todbot/blinkm2/schematic/blinkm_mk2c.brd

## EAGLE design schematic/blinkm_mk2c.brd (2014-01-24)

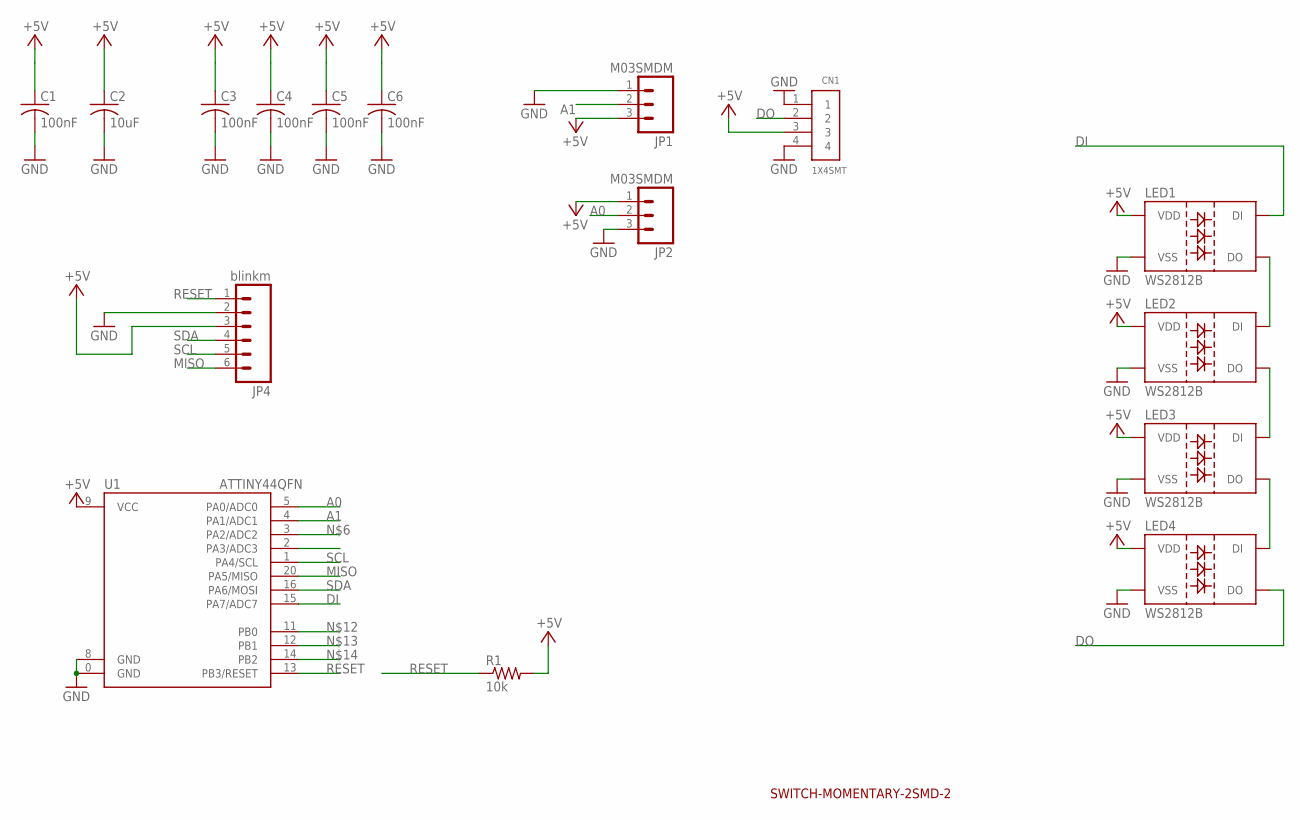
[picture p14: schematic blinkm_mk2c.sch]

Parts:
C1, C3, C4, C5, C6: 100nF; C0603
C2: 10uF; C0603
CN1: 1X4SMT; 1X4-SMT
JP1, JP2: M03SMDM; 1X03-SMD-MINIMAL
JP4: blinkm; 1X06_LOCK
LED1, LED2, LED3, LED4: WS2812B
R1: 10k; R0603
U1: ATTINY44QFN; QFN20

Connections:
+5V: C1.1, C2.1, C3.1, C4.1, C5.1, C6.1, CN1.3, JP1.3, JP2.1, JP4.3, LED1.1 (VDD), LED2.1 (VDD), LED3.1 (VDD), LED4.1 (VDD), R1.2, U1.9 (VCC)
A0: JP2.2, U1.5 (PA0/ADC0)
A1: JP1.2, U1.4 (PA1/ADC1)
DI: LED1.4 (DI), U1.15 (PA7/ADC7); also elsewhere on the board
DO: CN1.2, LED4.2 (DO)
GND: C1.2, C2.2, C3.2, C4.2, C5.2, C6.2, CN1.1, CN1.4, JP1.1, JP2.3, JP4.2, LED1.3 (VSS), LED2.3 (VSS), LED3.3 (VSS), LED4.3 (VSS), U1.0 (GND), U1.8 (GND); also elsewhere on the board
MISO: JP4.6, U1.20 (PA5/MISO)
unnamed: LED1.2 (DO), LED2.4 (DI)
unnamed: LED2.2 (DO), LED3.4 (DI)
unnamed: LED3.2 (DO), LED4.4 (DI)
RESET: JP4.1, R1.1, U1.13 (PB3/RESET)
SCL: JP4.5, U1.1 (PA4/SCL)
SDA: JP4.4, U1.16 (PA6/MOSI)

Notes on the sheet:
SWITCH-MOMENTARY-2SMD-2

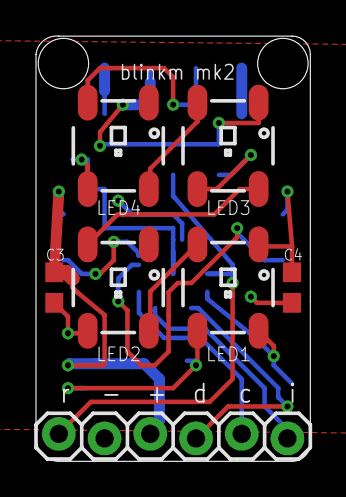
[picture p15: board blinkm_mk2c.brd from above]

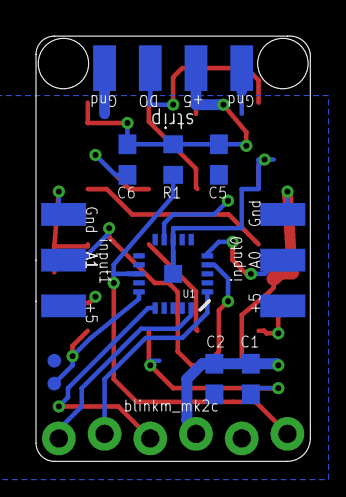
[picture p16: board blinkm_mk2c.brd from below]

Board: 2 copper layers, 15.2 x 23.6 mm, 18 parts (11 on the bottom side), 13 nets.

Other parts of the board:
TP1, TP2: TEST-POINT3; PAD.03X.03

Their connections:
DI: TP1.P$1; also elsewhere on the board
GND: TP2.P$1; also elsewhere on the board
