todbot/blinkm2/schematic/blinkm_mk2b.brd

## EAGLE design schematic/blinkm_mk2b.brd (2013-06-05)

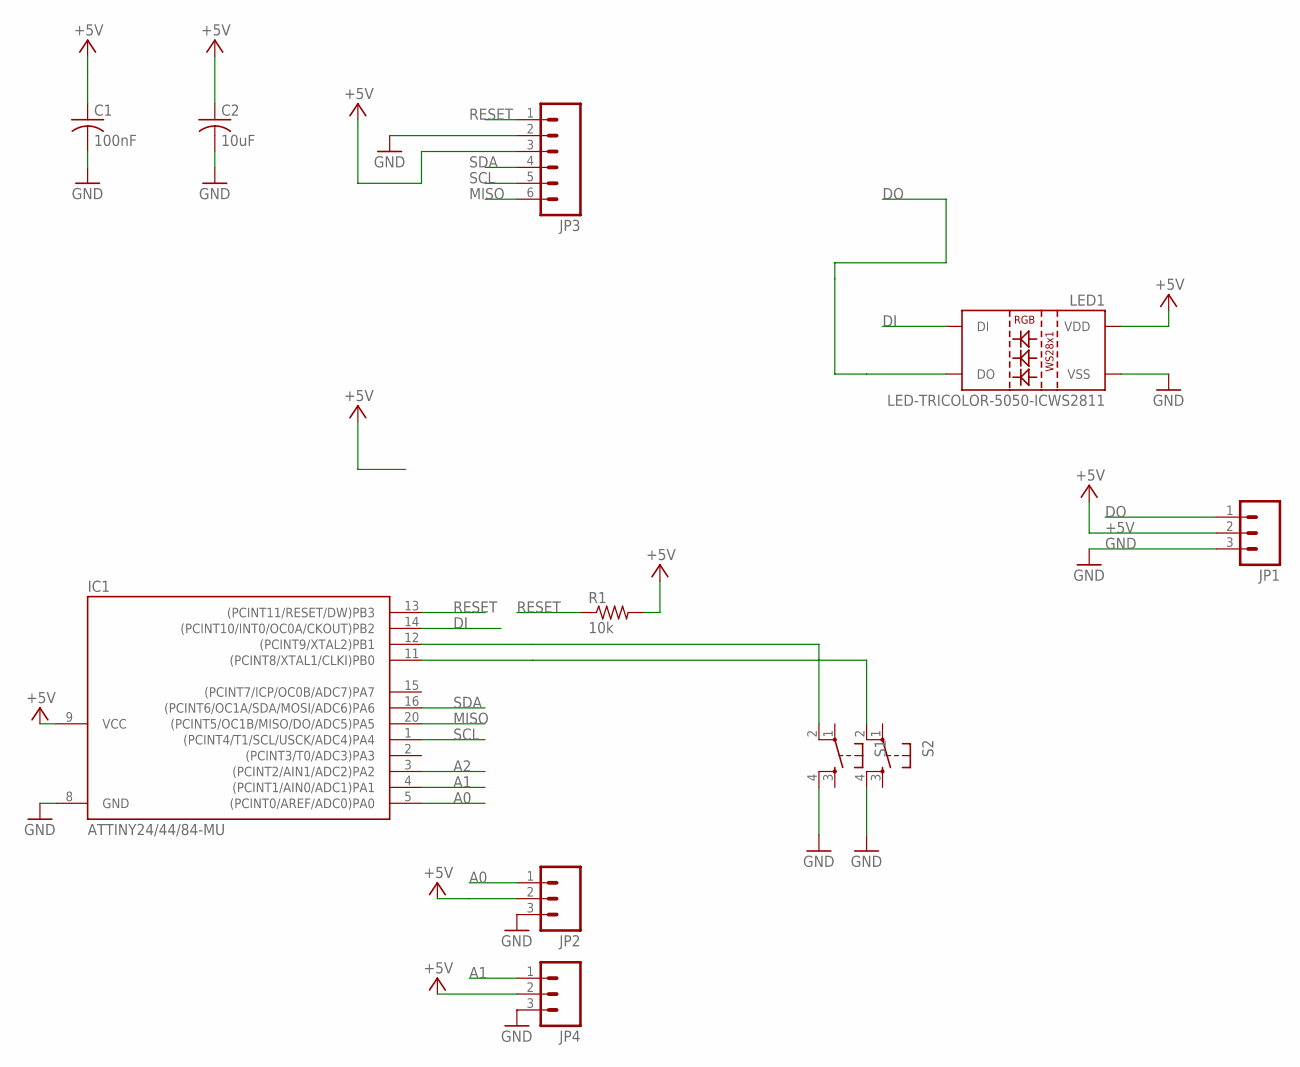
[picture p20: schematic blinkm_mk2b.sch]

Parts:
C1: 100nF; C0603
C2: 10uF; C0603
IC1: ATTINY24/44/84-MU; QFN/MLF20
JP1, JP2, JP4: M03PTH; 1X03
JP3: M06SIP; 1X06
LED1: LED-TRICOLOR-5050-ICWS2811; LED-TRICOLOR-5050-IC
R1: 10k; R0603
S1, S2: TAC_SWITCHSMD; TACTILE_SWITCH_SMD

Connections:
+5V: C1.1, C2.1, IC1.9 (VCC), JP1.2, JP2.2, JP3.3, JP4.2, LED1.3 (VDD), LED1.5 (VDD), R1.2
A0: IC1.5 ((PCINT0/AREF/ADC0)PA0), JP2.1
A1: IC1.4 ((PCINT1/AIN0/ADC1)PA1), JP4.1
A2: IC1.3 ((PCINT2/AIN1/ADC2)PA2)
DI: IC1.14 ((PCINT10/INT0/OC0A/CKOUT)PB2), LED1.2 (DI)
DO: JP1.1, LED1.1 (DO)
GND: C1.2, C2.2, IC1.8 (GND), JP1.3, JP2.3, JP3.2, JP4.3, LED1.6 (VSS), S1.4, S2.4
MISO: IC1.20 ((PCINT5/OC1B/MISO/DO/ADC5)PA5), JP3.6
unnamed: IC1.12 ((PCINT9/XTAL2)PB1), S1.2
unnamed: IC1.11 ((PCINT8/XTAL1/CLKI)PB0), S2.2
RESET: IC1.13 ((PCINT11/RESET/DW)PB3), JP3.1, R1.1
SCL: IC1.1 ((PCINT4/T1/SCL/USCK/ADC4)PA4), JP3.5
SDA: IC1.16 ((PCINT6/OC1A/SDA/MOSI/ADC6)PA6), JP3.4
