todbot/blinkm2/schematic/blinkm_mk2b.brd

## EAGLE design schematic/blinkm_mk2b.brd (continued)

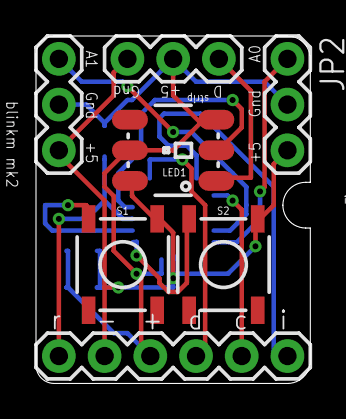
[picture p21: board blinkm_mk2b.brd from above]

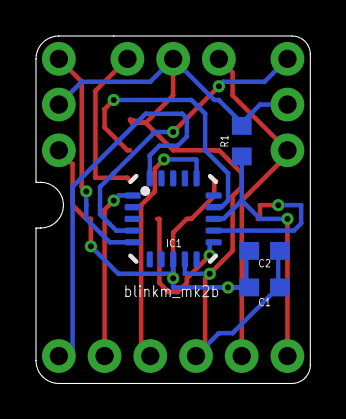
[picture p22: board blinkm_mk2b.brd from below]

Board: 2 copper layers, 15.2 x 19.3 mm, 11 parts (4 on the bottom side), 12 nets.
