todbot/blinkm2/sketches/BlinkMmk2Demo/BlinkMmk2Demo.ino

 /**
  *
  * NOTE: Pullup resistors should be used on SDA & SCL lines
  * 
  * Thanks to BroHogan for TinyWireS: http://playground.arduino.cc/Code/USIi2c
  * Credit and thanks to Don Blake for his usiTwiSlave code. 
  * More on TinyWireS usage - see TinyWireS.h
  *
  * 2015, Tod E. Kurt, http://todbot.com/blog/ http://thingm.com/
  *
  */

#if defined(__AVR_ATtiny85__) || defined(__AVR_ATtiny84__)  //
#define __BLINKM_BOARD__
#endif

#if defined(__BLINKM_BOARD__)
//#include "TinyWireS.h" // must comment out when in UNO debug
#else
#include "Wire.h"        // must comment out when in production
#endif

#include <Adafruit_NeoPixel.h>

#include "led_utils.h"

#define patt_max 16  // FIXME:

#include "patterns.h"  // the light sequence patterns


#if defined(__AVR_ATtiny85__)
// BlinkM pins
const int redPin = 3;  // 
const int grnPin = 4;  //
const int bluPin = 1;  // PWM, will blink when programming
const int sdaPin = 0;  // PWM, 'd' pin, can be digital I/O
const int sclPin = 2;  // A/D, 'c' pin, can be digital I/O, or analog input
const int LED_PIN = bluPin;
#elif defined(__AVR_ATtiny84__) || defined(__AVR_ATtiny44__)
// BlinkM MaxM pins 
const int redPin = 8;   // PB2 OC0A
const int grnPin = 7;   // PA7 OC0B
const int bluPin = 5;   // PA5 OC1B 'i' pin
const int sdaPin = 6;   // PA6 
const int sclPin = 9;   // PA4
const int in0Pin = A0;  // PA0
const int in1Pin = A1;  // PA1
const int in2Pin = A2;  // PA2
const int in3Pin = A3;  // PA3
const int LED_PIN = redPin;
#else
#warning "unknown board type, assuming UNO"
const int redPin = 9;
const int grnPin = 10;
const int bluPin = 11;
const int LED_PIN = 6;
#endif

/*
// ATMEL ATTINY84 / ARDUINO
//
//                           +-\/-+
//                     VCC  1|    |14  GND
//             (D 10)  PB0  2|    |13  AREF (D  0)
//             (D  9)  PB1  3|    |12  PA1  (D  1) 
//                     PB3  4|    |11  PA2  (D  2) 
//  PWM  INT0  (D  8)  PB2  5|    |10  PA3  (D  3) 
//  PWM        (D  7)  PA7  6|    |9   PA4  (D  4) 
//  PWM        (D  6)  PA6  7|    |8   PA5  (D  5)        PWM
//                           +----+
*/


#define I2C_ADDR  0x09     // default BlinkM addr
#define NUM_LEDS 8

#define patt_max 16  // FIXME:

// eeprom begin: muncha buncha eeprom
uint8_t  ee_i2c_addr         EEMEM = I2C_ADDR;
uint8_t  ee_boot_mode        EEMEM = 0x00; // FIXME: BOOT_PLAY_SCRIPT;
uint8_t  ee_boot_script_id   EEMEM = 0x00;
uint8_t  ee_boot_reps        EEMEM = 0x00;
uint8_t  ee_boot_fadespeed   EEMEM = 0x08;
uint8_t  ee_boot_timeadj     EEMEM = 0x00;
uint8_t  ee_unused2          EEMEM = 0xDA;

// NOTE: can't declare EEPROM statically because Arduino loader doesn't send eeprom
patternline_t patternlines_ee[patt_max] EEMEM;

byte cmd;
byte cmdargs[8];

uint8_t script_id;
uint8_t playpos   = 0; // current play position
uint8_t playstart = 0; // start play position
uint8_t playend   = patt_max; // end play position
uint8_t playcount = 0; // number of times to play loop, or 0=infinite
uint8_t playing; // playing values: 0=off, 1=normal, 2=playing from powerup playing=3 direct led addressing FIXME: 

uint16_t fade_millis;

patternline_t pltmp;  // temp pattern holder
//patternline_t* p;
uint16_t ttmp;   // temp time holder
uint8_t ntmp;    // temp ledn holder

CRGB curr;    // current/start color
CRGB dest;    // destination color
CRGB ctmp;    // temporary color
fract16 overlay_amount;
fract16 overlay_inc;
fract16 overlay_amounts[NUM_LEDS];
fract16 overlay_incs[NUM_LEDS];

const uint32_t led_update_millis = 10;  // tick msec
uint32_t led_update_next;
uint32_t pattern_update_next;

Adafruit_NeoPixel strip = Adafruit_NeoPixel(NUM_LEDS, LED_PIN, NEO_GRB + NEO_KHZ800);

uint8_t ledtoggle;  // temp debug

static void play_script();
static void get_next_patternline();
static void update_led_state();
static void check_i2c();
static void handle_script_cmd();

//
void setup()
{
  strip.begin();
  strip.show(); // Initialize all pixels to 'off'
  strip.setBrightness(128);

#if defined(__BLINKM_BOARD__)
  TinyWireS.begin(I2C_ADDR);
#else
  Wire.begin(I2C_ADDR);
  Serial.begin(115200);
  Serial.println("BlinkMmk2Demo!");
#endif
  
  // load up EEPROM from flash, 
  // to deal with fact that Arduino uploader doesn't upload EEPROM
  for( uint8_t i=0; i<patt_max; i++ ) {
    memcpy_P( &pltmp, &(patternlines_default[i]), sizeof(patternline_t) ); 
    eeprom_write_block( &pltmp, &(patternlines_ee[i]), sizeof(patternline_t) );
  }

  //  FIXME: check for play on boot
  script_id = 4;
  play_script();

}

//
void loop()
{
  update_led_state();
  check_i2c();
}


//
static void update_leds()
{
  if( overlay_amount < 250 ) { // 97.6% arbitrary
    ctmp = blend( curr, dest, (overlay_amount) );
    //ctmp = blend( curr, dest, (overlay_amount>>8) );
    //ctmp = dest;
    overlay_amount += overlay_inc;
  }
  else {
    ctmp = dest;
  }

  // for now set all pixels to same color
  for( uint8_t i=0; i< NUM_LEDS; i++) {
    strip.setPixelColor( i, ctmp.r, ctmp.g, ctmp.b );
  }
  strip.show();

}


//
// updateLEDState() is the main user-land function that:
// - periodically calls the rgb fader code to fade any actively moving colors
// - controls sequencing of a light pattern, if playing
// - ///triggers pattern playing on USB disconnect
//
static void update_led_state()
{
    uint32_t now = millis();
    
    // update LEDs every led_update_millis
    if( (long)(now - led_update_next) > 0 ) {
      led_update_next += led_update_millis;
      
      update_leds();
      
    } // led_update_next

    // playing light pattern
    if( playing ) {
      if( (long)(now - pattern_update_next) > 0  ) { // time to get next line
        digitalWrite(grnPin, (ledtoggle++)%2 );
        
        get_next_patternline();
        
        // prepare to go to next line
        playpos++;
        if( playpos == playend ) {
          playpos = playstart; // loop the pattern
          //playcount--;
          //if( playcount == 0 ) {
          //  playing=0; // done!
          //} else if(playcount==255) {
          //  playcount = 0; // infinite playing
          //}
        }
        pattern_update_next += ttmp;
      }
    } // playing
    
}

// compute the overlay_inc
// this is the amount overlay_amount is incremented every led_update_millis
//
// (led_update_millis / fade_millis) = fractional amount to do every tick
// e.g. (10 / 500) = 0.02; (10 / 1000) = 0.01
//
// (led_update_millis / fade_millis) * 256  = fract8 amount to add to overlay
// (led_update_millis / fade_millis) * 65536  = fract16 amount to add to overlay
// 
// => overlay_inc = 65536 * led_update_millis / fade_millis 
//
static void calculate_overlay_inc()
{
  overlay_amount = 0;
  //overlay_inc = ((uint32_t)65536 * led_update_millis) / fade_millis;
  overlay_inc = ((uint16_t)256 * led_update_millis) / fade_millis;
}

//
static void play_script()
{
  if( script_id == 0 ) {
    playend = 5;  // FIXME:
    playcount = 0;  // FIXME: infinite
  }
  else { 
    playend = pgm_read_byte( &pattern_lens[script_id] ); 
    playcount = 0;
  }
  
  playpos = 0;
  playing = 1;

  get_next_patternline();
}

//
static void get_next_patternline()
{
  if( script_id == 0 ) { // eeprom
    eeprom_read_block(&pltmp, &patternlines_ee[playpos],sizeof(patternline_t));
  } else {
    patternline_t* p;
    memcpy_P( &p, &patterns[script_id], sizeof(patternline_t*) ); // read in start addr of patternline set
    memcpy_P(&pltmp, &p[playpos], sizeof(patternline_t));  // read in patternline
  }
  cmd  = pltmp.cmd;
  ctmp = pltmp.color;
  ttmp = pltmp.dmillis * 10;
  ntmp = pltmp.ledn;
  
  if( ttmp == 0 && ctmp.r==0 && ctmp.g==0 && ctmp.b==0 ) {
    // skip lines set to zero
  }
  else {
    handle_script_cmd();
  }
}


//
static void handle_script_cmd()
{
  Serial.print("handle_script_cmd:"); Serial.println((char)cmd);
  if( cmd == 'n' ) {
    dest = ctmp;
    curr = ctmp;
  }
  else if( cmd == 'c' ) { 
    curr = dest;
    dest = ctmp;
    fade_millis = ttmp / 2;      //fade_millis = ttmp;
    calculate_overlay_inc();
  }
  else if( cmd == 'C' ) {
      byte dr = cmdargs[0];
      byte dg = cmdargs[1];
      byte db = cmdargs[2];
      curr.r = curr.r + (random8() % dr ) - (dr/2);  // random around previsous color
      curr.g = curr.g + (random8() % dg ) - (dg/2);
      curr.b = curr.b + (random8() % db ) - (db/2);
      dest = curr;
  }
  else if( cmd == 'h' ) {
    curr = dest;
    hsv2rgb_rainbow( (const CHSV&)(ctmp), dest ); // FIXME: test
    Serial.print("h:");Serial.print(cmdargs[0]); Serial.print("r:"); Serial.println(dest.r);
    fade_millis = ttmp / 2;
    calculate_overlay_inc();
  }
  else if( cmd == 'H' ) {
  }
  else if( cmd == 'p' ) {
  }
  else if( cmd == 'f' ) {
  }
  else if( cmd == 't' ) {
  }
  else if( cmd == 'F' ) {
  }
  else if( cmd == 'j' ) {
  }
  else if( cmd == 'i' ) {
  }
  else if( cmd == 'I' ) {
  }
  else if( cmd == 'k' ) {
  }
  else if( cmd == 'K' ) {
  }

}

// --------------------------------------------------------

//
static void read_i2c_vals(uint8_t num, uint8_t*buf)
{
#if defined(__BLINKM_BOARD__)
  for( uint8_t i=0; i<num; i++)
    buf[i] = TinyWireS.receive();
#else
  for( uint8_t i=0; i<num; i++)
    buf[i] = Wire.read();
#endif
}

//
static void check_i2c()
{
#if defined(__BLINKM_BOARD__)
  if( TinyWireS.available() ) { 
    cmd = TinyWireS.receive();    // first byte is command
#else
  if( Wire.available() ) { 
    cmd = Wire.read();    // first byte is command
#endif
    
    if( cmd == 'n' ||
        cmd == 'c' ||
        cmd == 'C' ||
        cmd == 'h' ||
        cmd == 'H' ||
        cmd == 'p' ) {
      read_i2c_vals( 3, cmdargs );
      handle_script_cmd();
    }
    else if( cmd == 'f' ) {
      
    }
    // else if( cmd == 'h' ) { // "fade to HSB color" cmd
    //}
    else {
      // unknown cmd
    }

  }
}

/*
//
void updateLEDsNew()
{
  for( int i = 0; i<NUM_LEDS; i++ ) {
    overlay_amount = overlay_amounts[i];
    overlay_inc = overlay_incs[i];
    if( overlay_amount < 250 ) { // 97.6% arbitrary
      ctmp = blend( curr, dest, (overlay_amount) );
      //ctmp = blend( curr, dest, (overlay_amount>>8) );
      //ctmp = dest;
      overlay_amount += overlay_inc;
    }
    else {
      ctmp = dest;
    }

    strip.setPixelColor( i, ctmp.r, ctmp.g, ctmp.b );
  }
  strip.show();

}
*/
